JDJelectronics/The-Mesh3310-Project/Kicad_Mesh3310/3D_models/FPC-SMD_FH12-24S-0.5SH-55.step

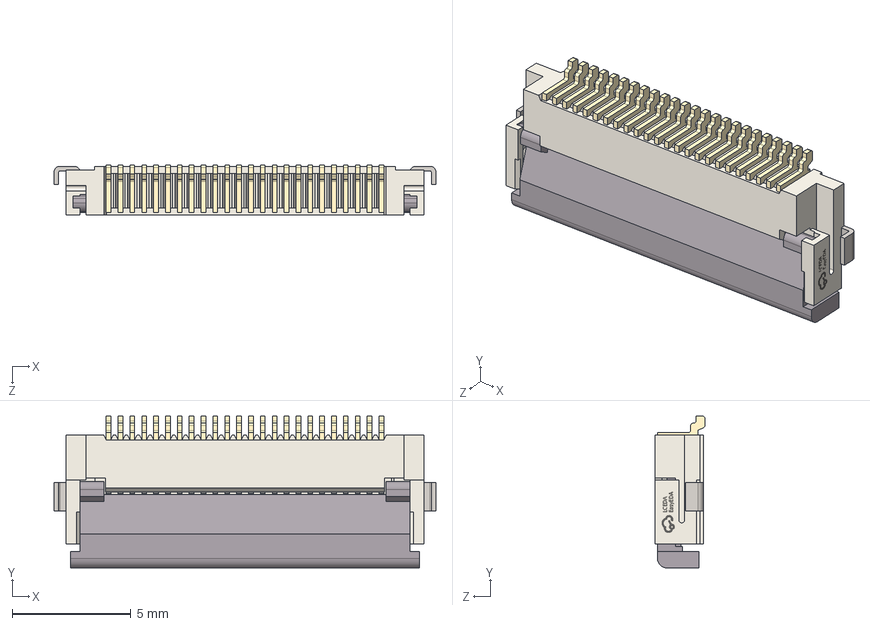
[picture p18: CAD file, 2026-01-23]
Kicad_Mesh3310/3D_models/FPC-SMD_FH12-24S-0.5SH-55.step
16.1 x 6.40 x 2.10 mm
