JDJelectronics/The-Mesh3310-Project/Kicad_Mesh3310/3D_models/RA-01H--3DModel-STEP-1.STEP

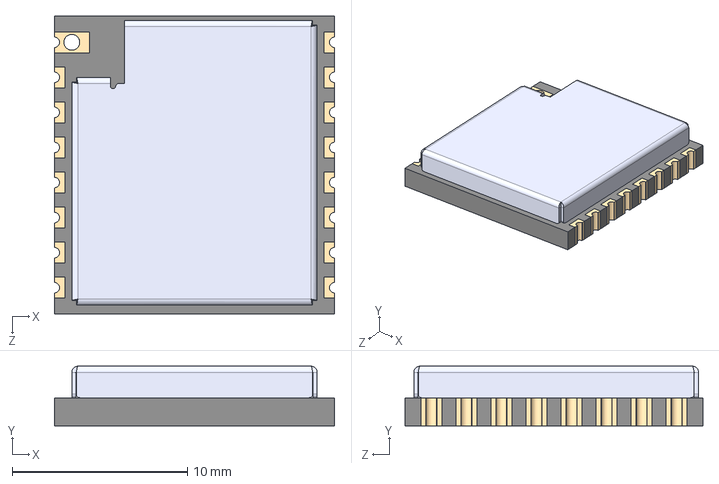
[picture p19: CAD file, 2026-01-23]
Kicad_Mesh3310/3D_models/RA-01H--3DModel-STEP-1.STEP
16.0 x 3.40 x 17.0 mm
