JDJelectronics/The-Mesh3310-Project/Kicad_Mesh3310/3D_models/SOIC-8_L4.9-W3.9-H1.7-LS6.0-P1.27.step

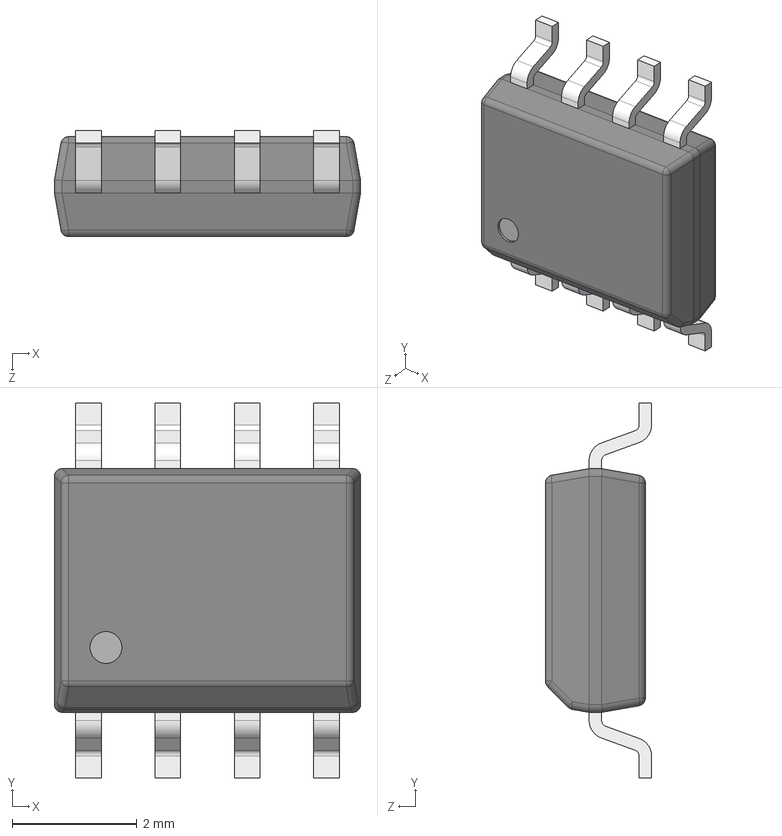
[picture p20: CAD file, 2026-01-23]
Kicad_Mesh3310/3D_models/SOIC-8_L4.9-W3.9-H1.7-LS6.0-P1.27.step
4.90 x 6.00 x 1.70 mm
