JDJelectronics/The-Mesh3310-Project/Kicad_Mesh3310/3D_models/VSON-14_L4.0-W3.0-H1.0-P0.50.step

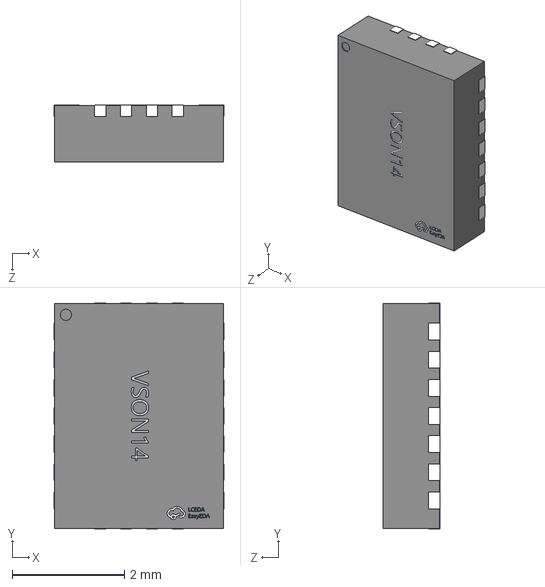
[picture p21: CAD file, 2026-01-23]
Kicad_Mesh3310/3D_models/VSON-14_L4.0-W3.0-H1.0-P0.50.step
3.02 x 4.02 x 1.01 mm
