JDJelectronics/The-Mesh3310-Project/Kicad_Mesh3310/3D_models/IND-SMD_L6.0-W6.0-H4.5.step

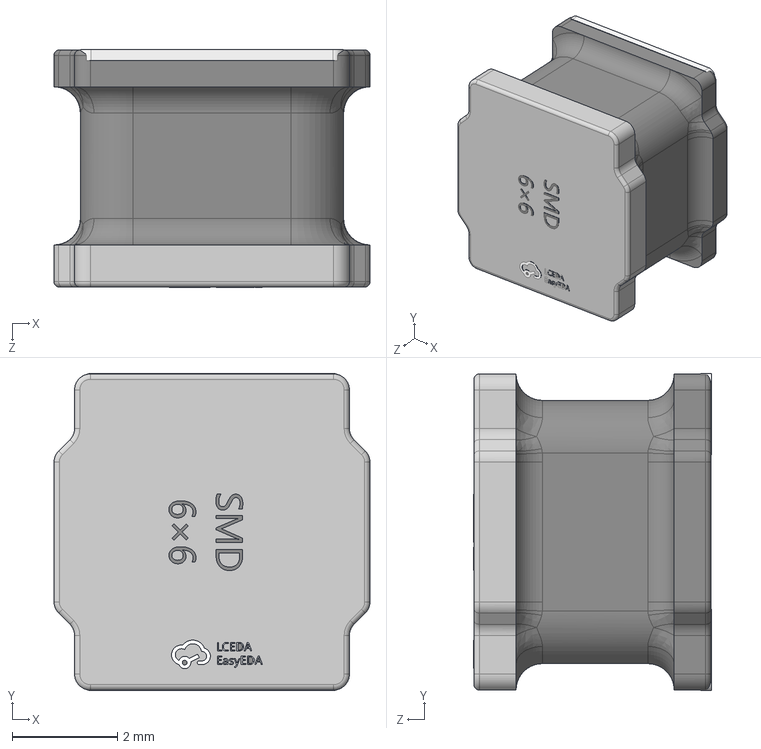
[picture p22: CAD file, 2026-01-23]
Kicad_Mesh3310/3D_models/IND-SMD_L6.0-W6.0-H4.5.step
6.00 x 6.02 x 4.52 mm
