JDJelectronics/The-Mesh3310-Project/Kicad_Mesh3310/3D_models/AQFN-73_L7.0-W7.0-H0.9-P0.50.step

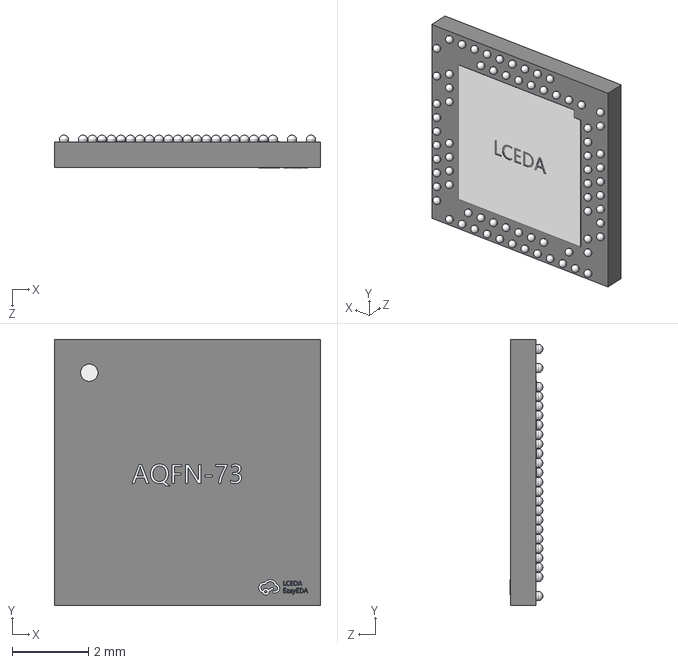
[picture p23: CAD file, 2026-01-23]
Kicad_Mesh3310/3D_models/AQFN-73_L7.0-W7.0-H0.9-P0.50.step
7.00 x 7.00 x 0.865 mm
