JDJelectronics/The-Mesh3310-Project/Kicad_Mesh3310/3D_models/SOT-23-3P_L2.9-W1.3-H1.0-LS2.4-P0.95.step

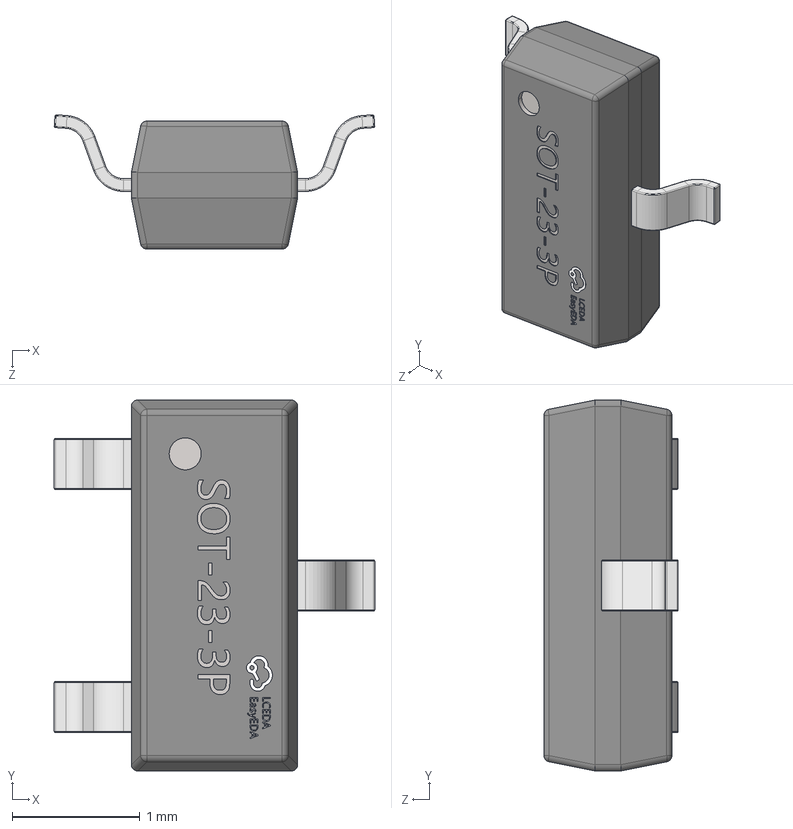
[picture p24: CAD file, 2026-01-23]
Kicad_Mesh3310/3D_models/SOT-23-3P_L2.9-W1.3-H1.0-LS2.4-P0.95.step
2.51 x 2.90 x 1.05 mm
