JDJelectronics/The-Mesh3310-Project/Kicad_Mesh3310/3D_models/CONN-SMD_HCZZ0032-4.step

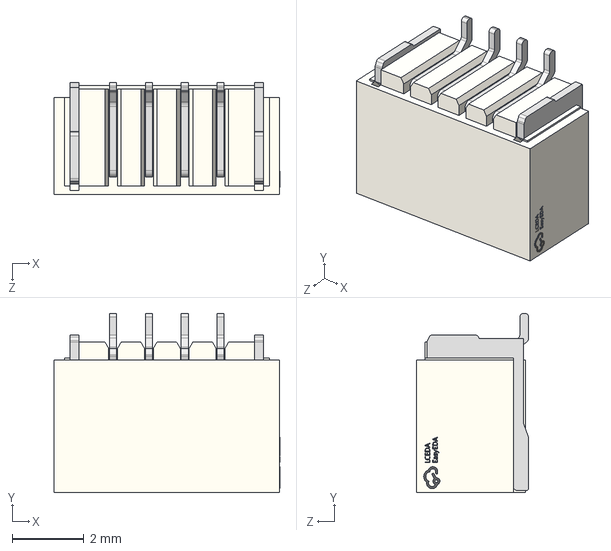
[picture p25: CAD file, 2026-01-23]
Kicad_Mesh3310/3D_models/CONN-SMD_HCZZ0032-4.step
6.31 x 5.00 x 3.14 mm
