JDJelectronics/The-Mesh3310-Project/Kicad_Mesh3310/3D_models/WQFN-48_L6.0-W6.0-P0.40-BL-EP4.6.step

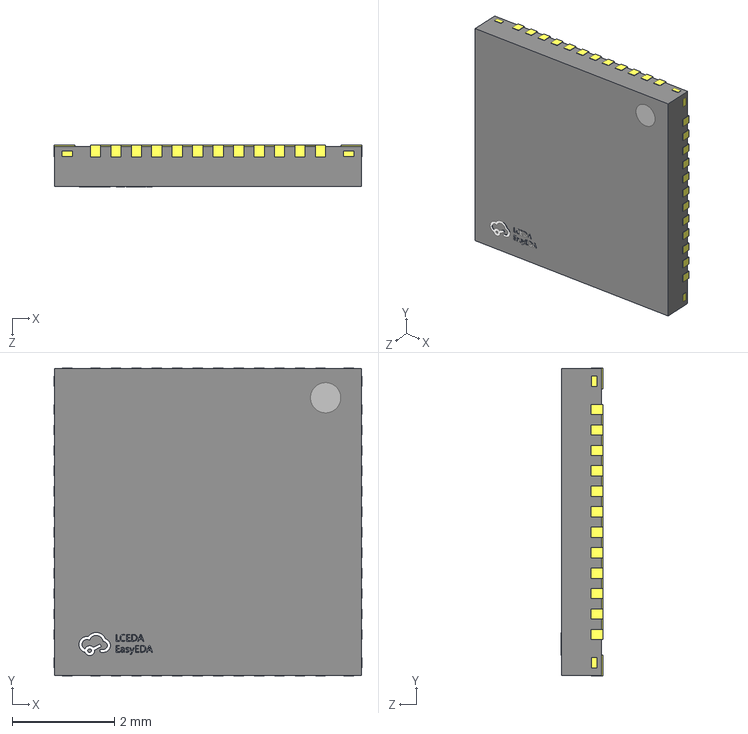
[picture p26: CAD file, 2026-01-23]
Kicad_Mesh3310/3D_models/WQFN-48_L6.0-W6.0-P0.40-BL-EP4.6.step
6.02 x 6.02 x 0.825 mm
