JDJelectronics/The-Mesh3310-Project/Kicad_Mesh3310/3D_models/SOT-666-6P_L1.6-W1.2-H0.6-LS1.6-P0.50.step

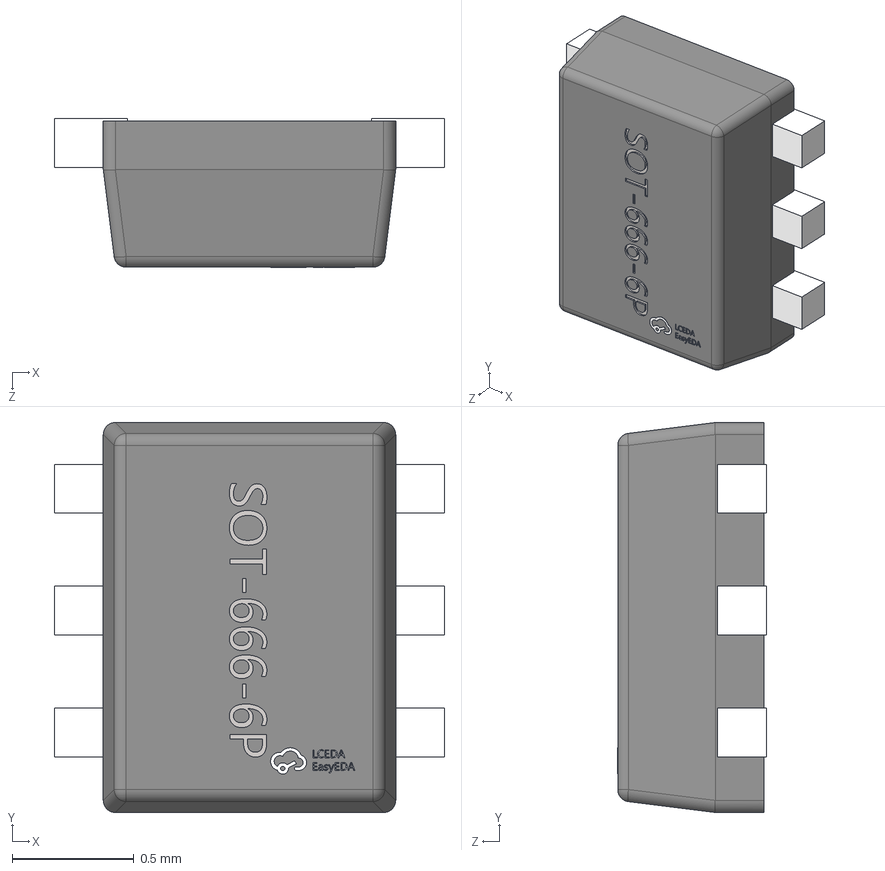
[picture p27: CAD file, 2026-01-23]
Kicad_Mesh3310/3D_models/SOT-666-6P_L1.6-W1.2-H0.6-LS1.6-P0.50.step
1.60 x 1.60 x 0.611 mm
