JDJelectronics/The-Mesh3310-Project/Kicad_Mesh3310/3D_models/SW-SMD_4P-L4.2-W3.4-H2.5-P2.15-LS5.2.step

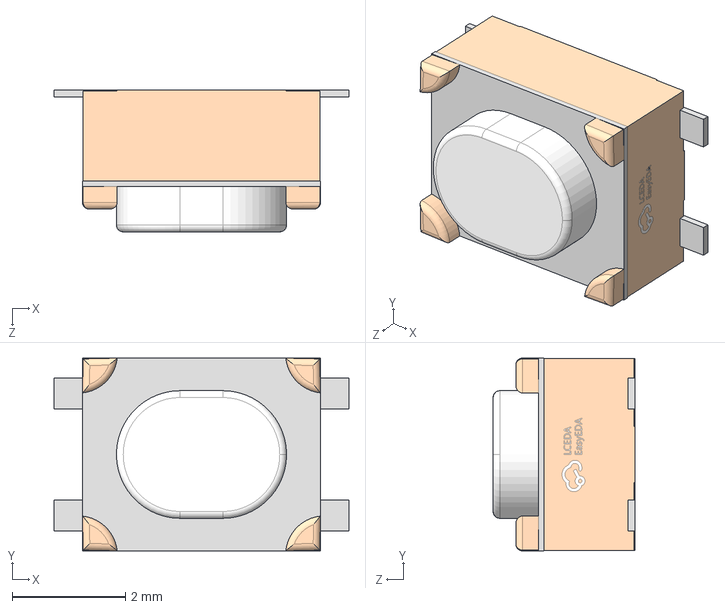
[picture p28: CAD file, 2026-01-23]
Kicad_Mesh3310/3D_models/SW-SMD_4P-L4.2-W3.4-H2.5-P2.15-LS5.2.step
5.20 x 3.40 x 2.50 mm
