JDJelectronics/The-Mesh3310-Project/Kicad_Mesh3310/3D_models/CONN-SMD_PH-2AWB.step

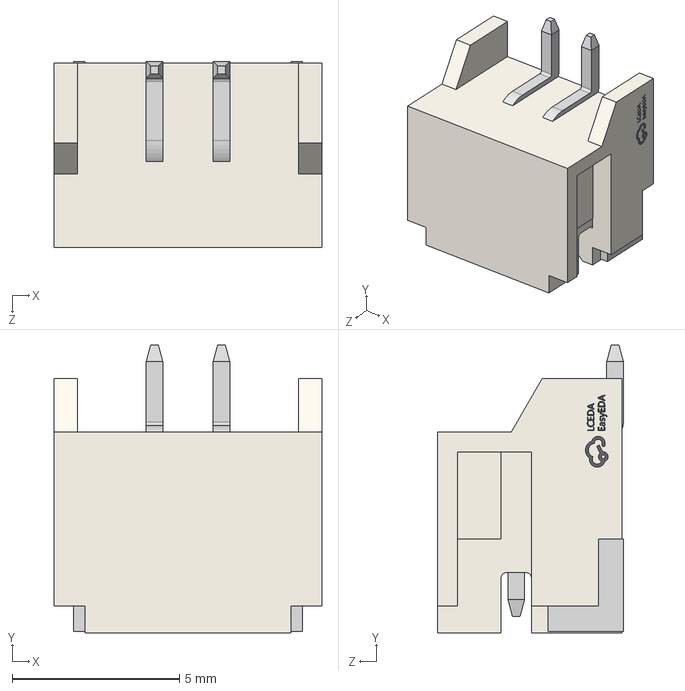
[picture p29: CAD file, 2026-01-23]
Kicad_Mesh3310/3D_models/CONN-SMD_PH-2AWB.step
8.00 x 8.60 x 5.55 mm
