JDJelectronics/The-Mesh3310-Project/Kicad_Mesh3310/3D_models/SOT-23-5_L2.9-W1.6-P0.95-LS2.8-BL.step

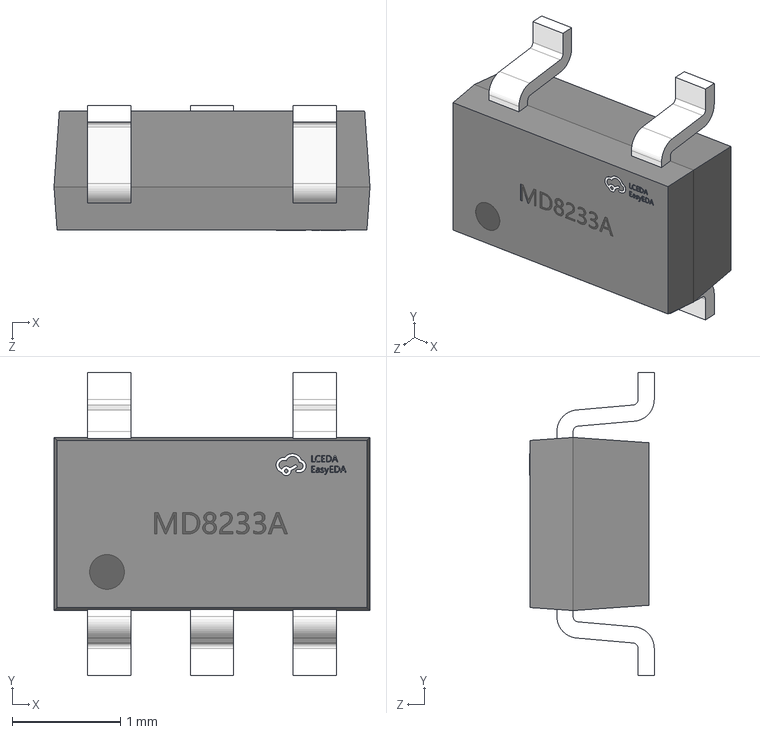
[picture p30: CAD file, 2026-01-23]
Kicad_Mesh3310/3D_models/SOT-23-5_L2.9-W1.6-P0.95-LS2.8-BL.step
2.92 x 2.80 x 1.15 mm
