JDJelectronics/The-Mesh3310-Project/Kicad_Mesh3310/3D_models/CONN-SMD_ZH1.5-WS-2P.step

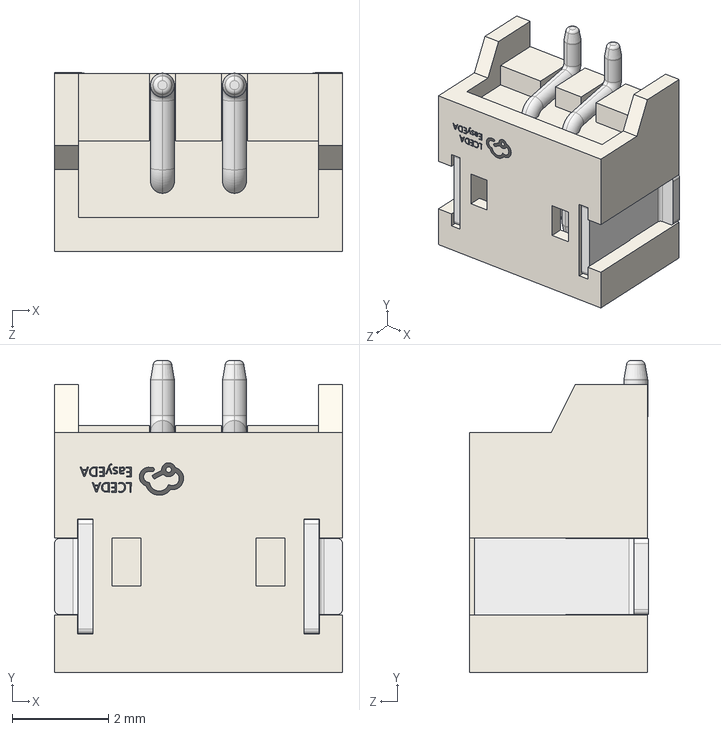
[picture p31: CAD file, 2026-01-23]
Kicad_Mesh3310/3D_models/CONN-SMD_ZH1.5-WS-2P.step
6.00 x 6.50 x 3.72 mm
