JDJelectronics/The-Mesh3310-Project/Kicad_Mesh3310/3D_models/WLCSP-94_L3.6-W3.5-P0.35-TL.step

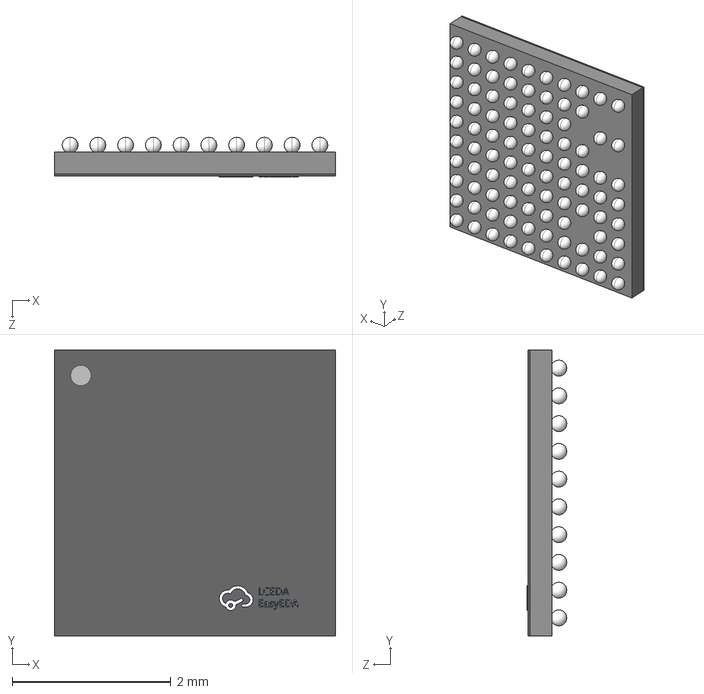
[picture p32: CAD file, 2026-01-23]
Kicad_Mesh3310/3D_models/WLCSP-94_L3.6-W3.5-P0.35-TL.step
3.54 x 3.61 x 0.499 mm
