JDJelectronics/The-Mesh3310-Project/Kicad_Mesh3310/3D_models/FILTER-SMD_10P-L2.0-W1.3-H1.0-P0.5.step

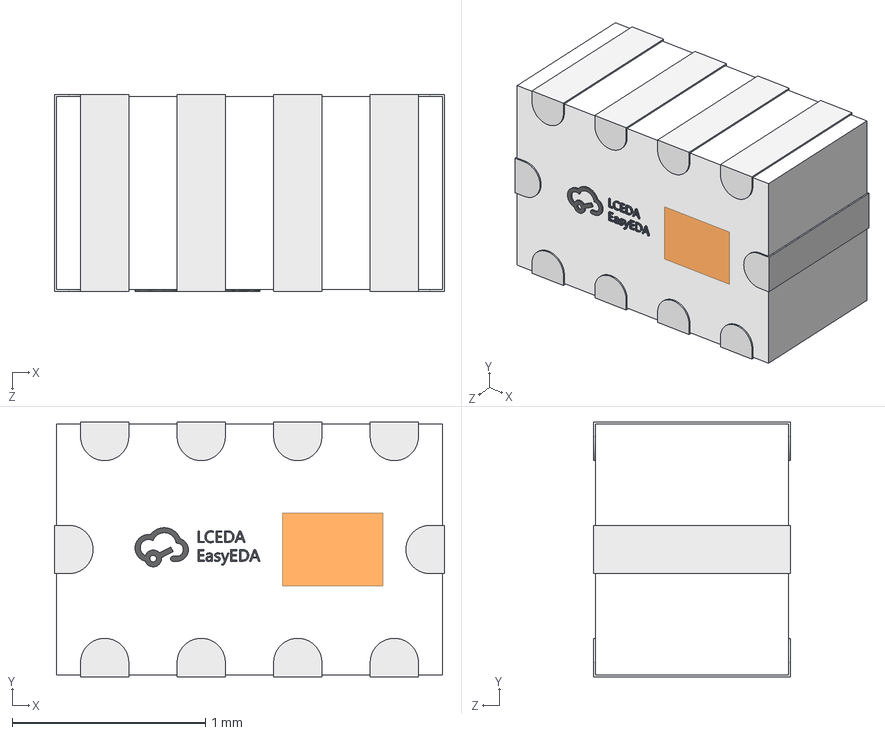
[picture p33: CAD file, 2026-01-23]
Kicad_Mesh3310/3D_models/FILTER-SMD_10P-L2.0-W1.3-H1.0-P0.5.step
2.02 x 1.32 x 1.02 mm
