JDJelectronics/The-Mesh3310-Project/Kicad_Mesh3310/3D_models/SW-SMD_4P-L5.1-W5.1-P3.70-LS6.5-TL_H1.5.step

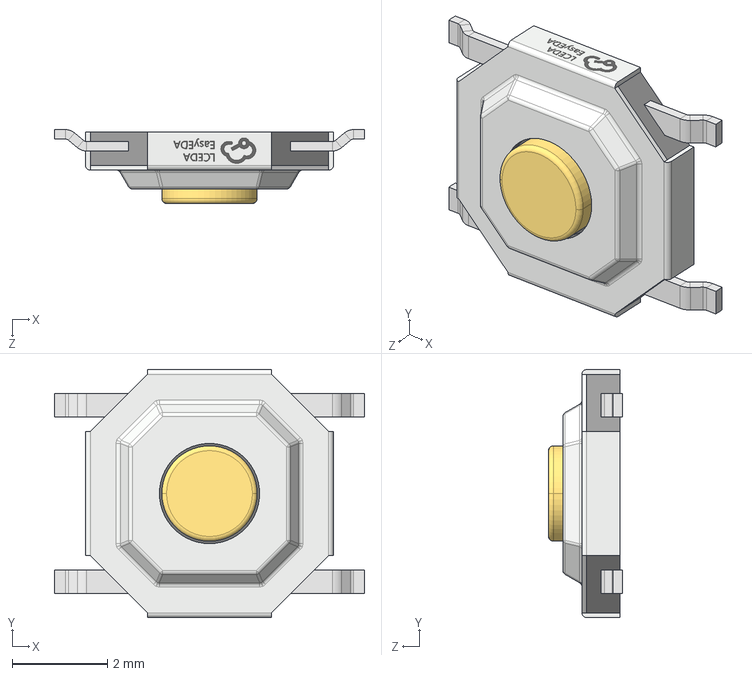
[picture p34: CAD file, 2026-01-23]
Kicad_Mesh3310/3D_models/SW-SMD_4P-L5.1-W5.1-P3.70-LS6.5-TL_H1.5.step
6.50 x 5.20 x 1.55 mm
