JDJelectronics/The-Mesh3310-Project/Kicad_Mesh3310/3D_models/UTDFN-4AL_L1.0-W1.0-H0.6-P0.65-BL.step

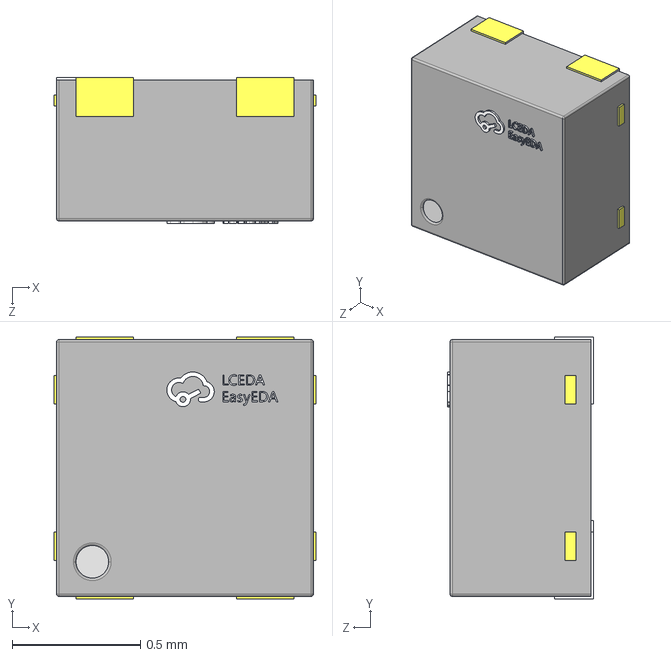
[picture p35: CAD file, 2026-01-23]
Kicad_Mesh3310/3D_models/UTDFN-4AL_L1.0-W1.0-H0.6-P0.65-BL.step
1.02 x 1.02 x 0.57 mm
