JDJelectronics/The-Mesh3310-Project/Kicad_Mesh3310/3D_models/TSNP-6_L1.1-W0.7-H0.4-P0.40-BL.step

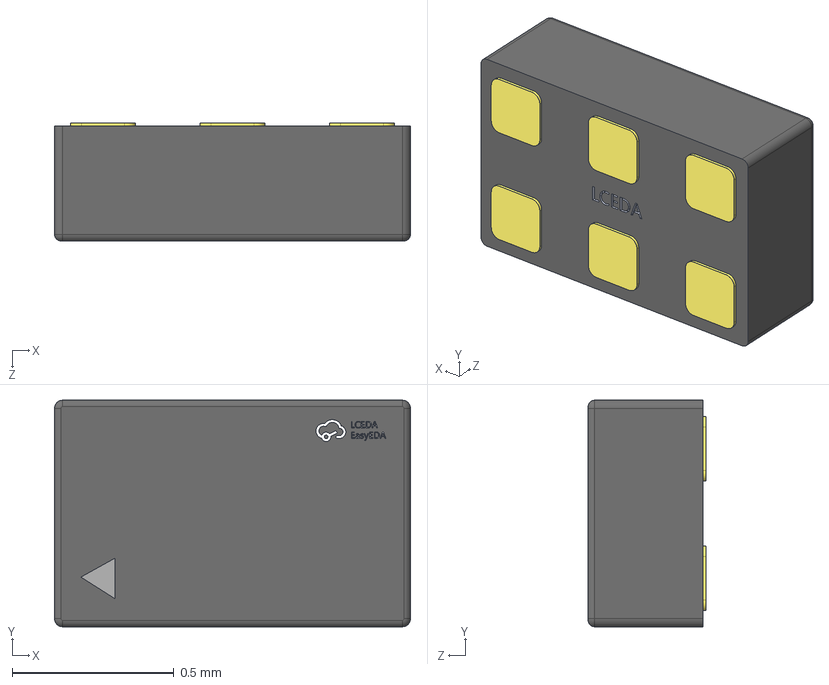
[picture p36: CAD file, 2026-01-23]
Kicad_Mesh3310/3D_models/TSNP-6_L1.1-W0.7-H0.4-P0.40-BL.step
1.10 x 0.7 x 0.366 mm
