JDJelectronics/The-Mesh3310-Project/Kicad_Mesh3310/3D_models/BUZ-SMD_4P-L8.5-W8.5-H3.0.step

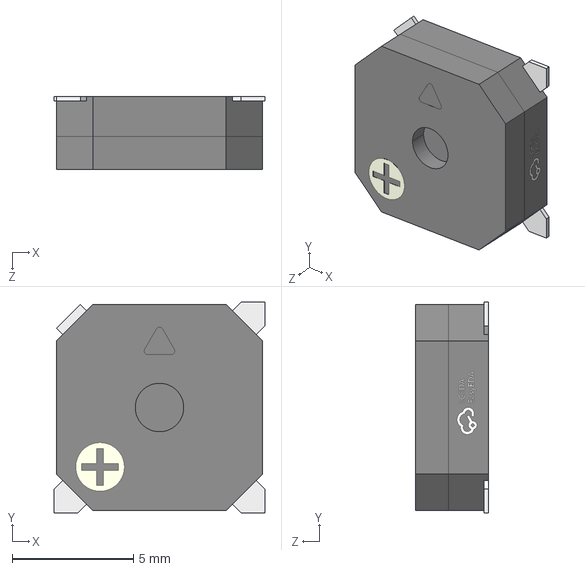
[picture p37: CAD file, 2026-01-23]
Kicad_Mesh3310/3D_models/BUZ-SMD_4P-L8.5-W8.5-H3.0.step
8.70 x 8.70 x 3.02 mm
