JDJelectronics/The-Mesh3310-Project/Kicad_Mesh3310/3D_models/SOT-363-6_L2.0-W1.25-LS2.1-BL.step

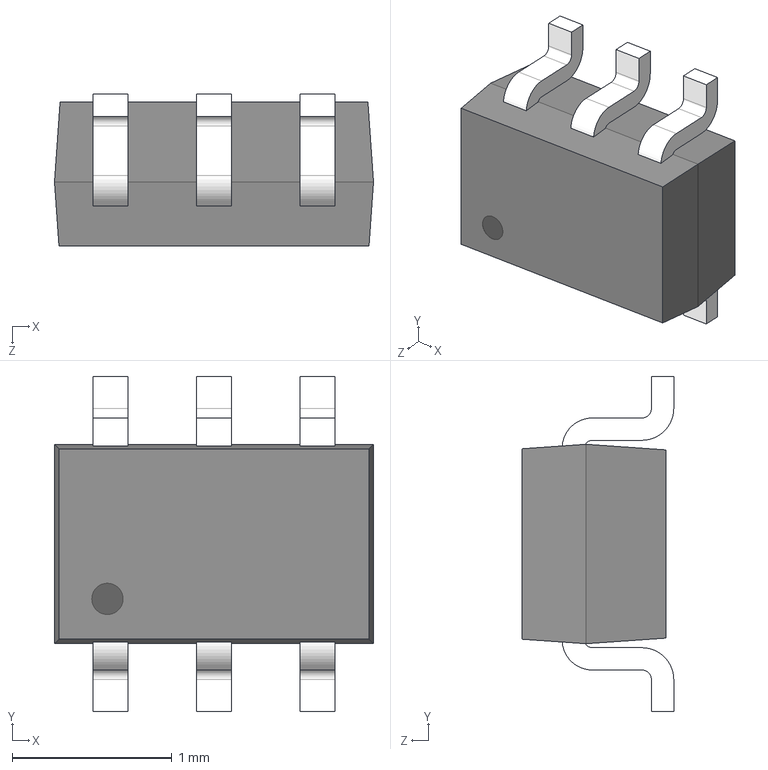
[picture p38: CAD file, 2026-01-23]
Kicad_Mesh3310/3D_models/SOT-363-6_L2.0-W1.25-LS2.1-BL.step
2.00 x 2.10 x 0.95 mm
