JDJelectronics/The-Mesh3310-Project/Kicad_Mesh3310/3D_models/QFN-24_L4.0-W4.0-H0.9-P0.50.step

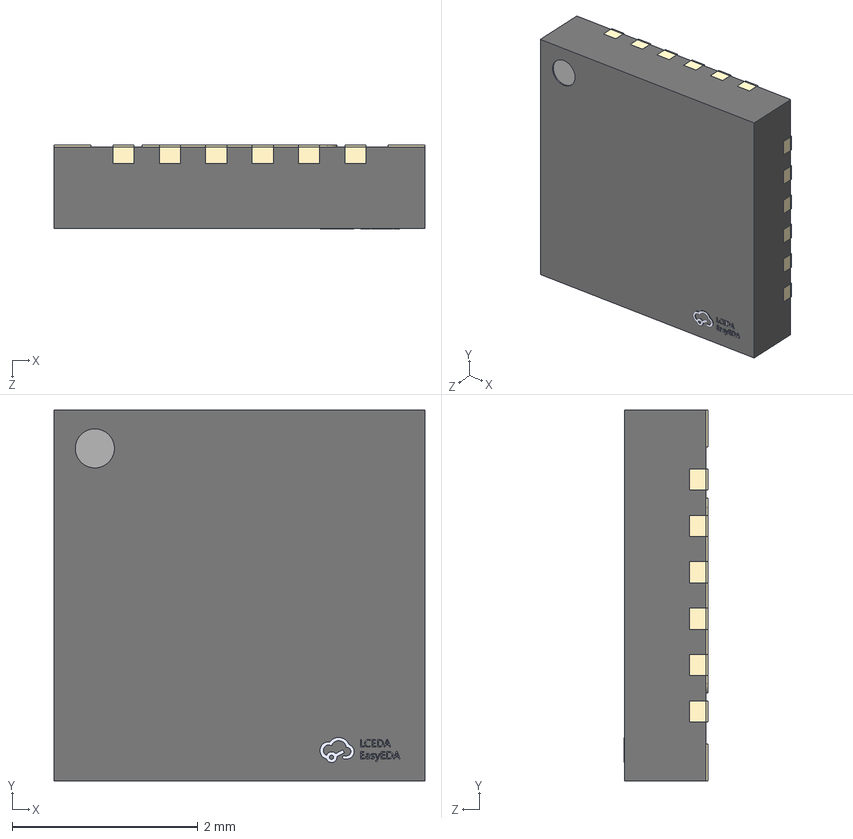
[picture p39: CAD file, 2026-01-23]
Kicad_Mesh3310/3D_models/QFN-24_L4.0-W4.0-H0.9-P0.50.step
4.00 x 4.00 x 0.91 mm
