JDJelectronics/The-Mesh3310-Project/Kicad_Mesh3310/3D_models/FC-135R_L3.2-W1.5.step

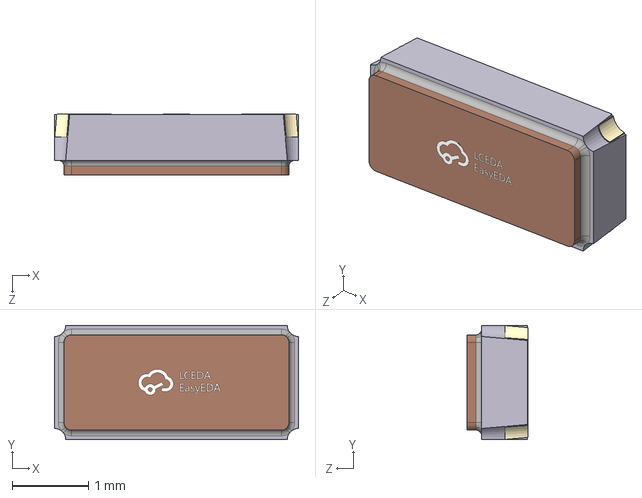
[picture p40: CAD file, 2026-01-23]
Kicad_Mesh3310/3D_models/FC-135R_L3.2-W1.5.step
3.20 x 1.50 x 0.801 mm
