JDJelectronics/The-Mesh3310-Project/Kicad_Mesh3310/3D_models/LED-ARRAY-SMD_4P-L1.6-W1.5-BR_XL-1615RGBC-RF.step

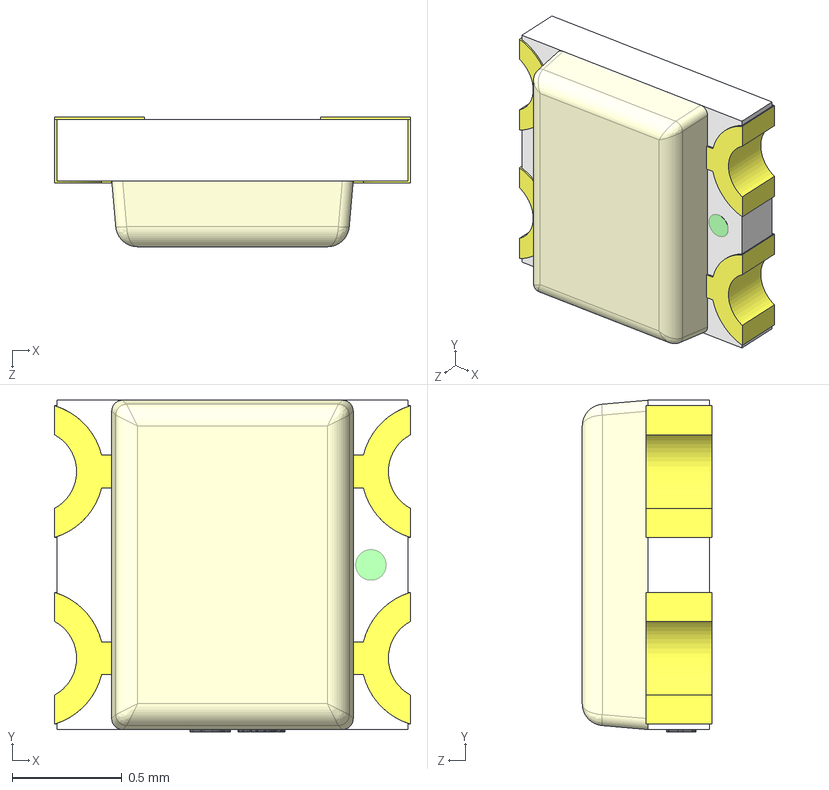
[picture p41: CAD file, 2026-01-23]
Kicad_Mesh3310/3D_models/LED-ARRAY-SMD_4P-L1.6-W1.5-BR_XL-1615RGBC-RF.step
1.62 x 1.51 x 0.59 mm
