JDJelectronics/The-Mesh3310-Project/Kicad_Mesh3310/3D_models/SW-SMD_8P-L7.0-W7.0-P1.40-LS7.4-TL.step

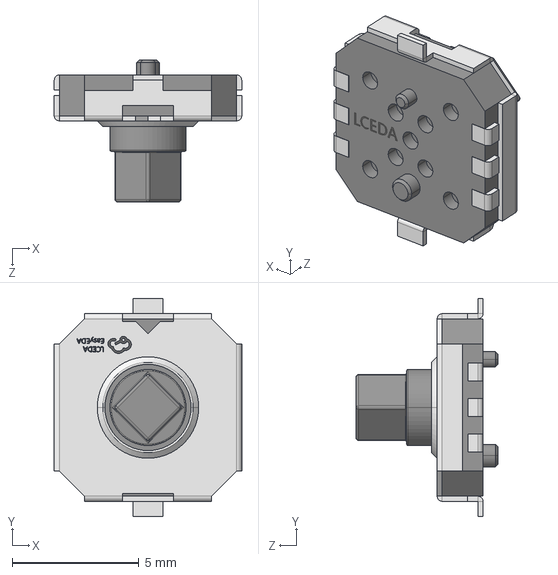
[picture p42: CAD file, 2026-01-23]
Kicad_Mesh3310/3D_models/SW-SMD_8P-L7.0-W7.0-P1.40-LS7.4-TL.step
7.40 x 8.60 x 5.60 mm
