JDJelectronics/The-Mesh3310-Project/Kicad_Mesh3310/3D_models/KEY-SMD_2P-L6.0-W6.0-H5.0-P6.00.step

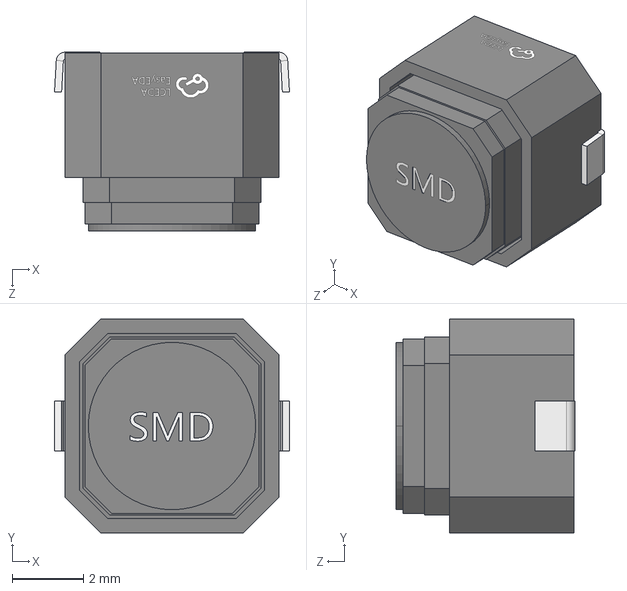
[picture p43: CAD file, 2026-01-23]
Kicad_Mesh3310/3D_models/KEY-SMD_2P-L6.0-W6.0-H5.0-P6.00.step
6.60 x 6.00 x 5.02 mm
