JDJelectronics/The-Mesh3310-Project/Kicad_Mesh3310/3D_models/IND-SMD_L4.2-W4.4-H2.0.step

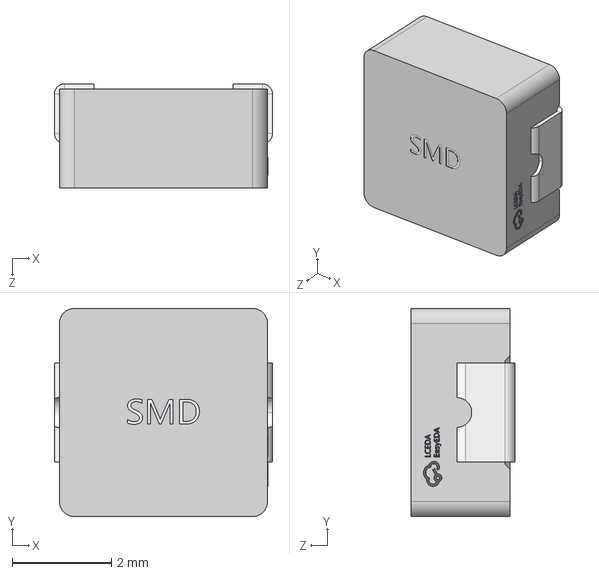
[picture p44: CAD file, 2026-01-23]
Kicad_Mesh3310/3D_models/IND-SMD_L4.2-W4.4-H2.0.step
4.40 x 4.20 x 2.10 mm
