JDJelectronics/The-Mesh3310-Project/Kicad_Mesh3310/3D_models/SMA_L4.3-W2.6-LS5.2-RD.step

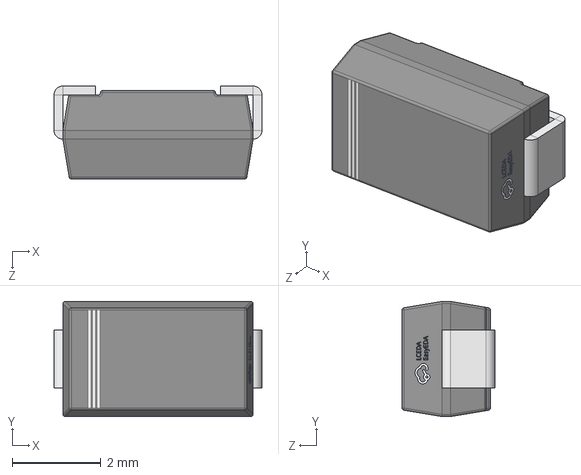
[picture p45: CAD file, 2026-01-23]
Kicad_Mesh3310/3D_models/SMA_L4.3-W2.6-LS5.2-RD.step
4.70 x 2.60 x 2.10 mm
