JDJelectronics/The-Mesh3310-Project/Kicad_Mesh3310/3D_models/LGA-14_L2.5-W3.0-H0.9-P0.50.step

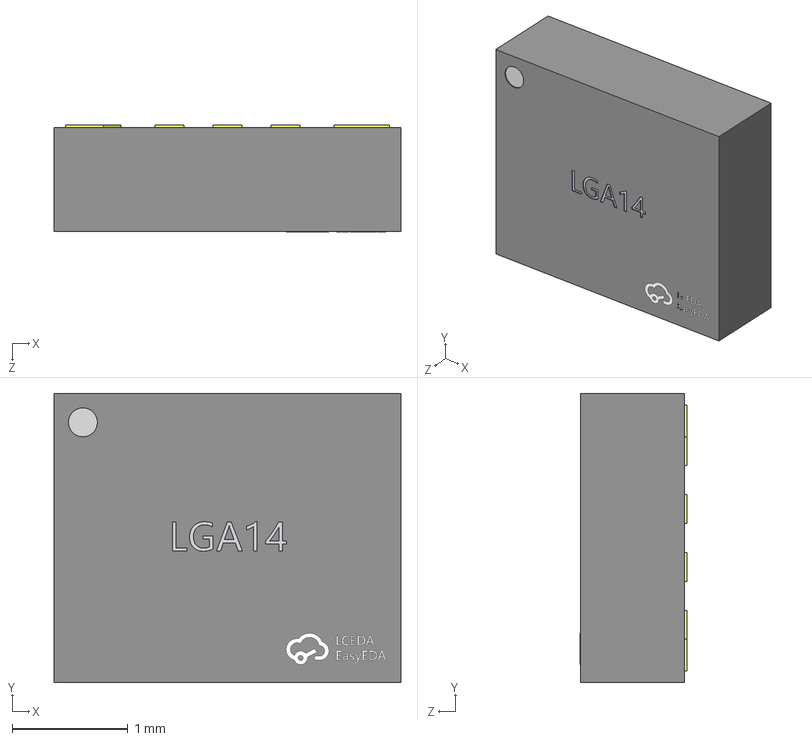
[picture p46: CAD file, 2026-01-23]
Kicad_Mesh3310/3D_models/LGA-14_L2.5-W3.0-H0.9-P0.50.step
3.00 x 2.50 x 0.921 mm
