JDJelectronics/The-Mesh3310-Project/Kicad_Mesh3310/3D_models/CRYSTAL-SMD_4P-L2.0-W1.6-BL.step

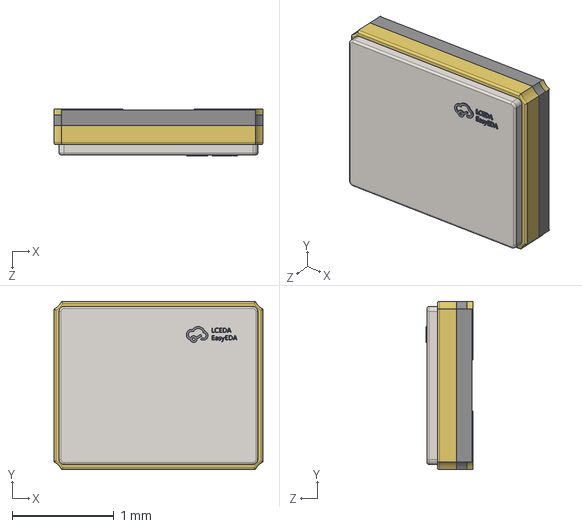
[picture p47: CAD file, 2026-01-23]
Kicad_Mesh3310/3D_models/CRYSTAL-SMD_4P-L2.0-W1.6-BL.step
2.05 x 1.65 x 0.46 mm
